ejkreboot/murmur/docs/images/Drawing3.png

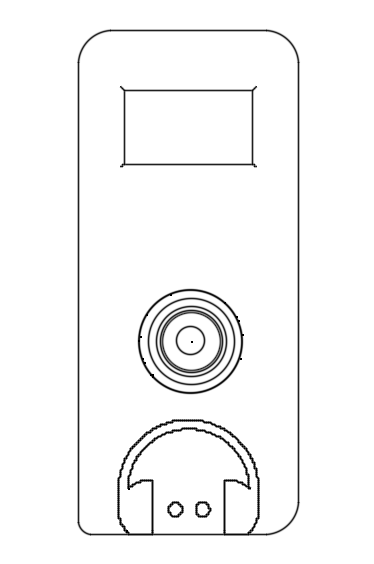
docs/images/Drawing3.png
